ahover307/ninja-receiver-and-timer/Pictures/Wiring Example.jpg

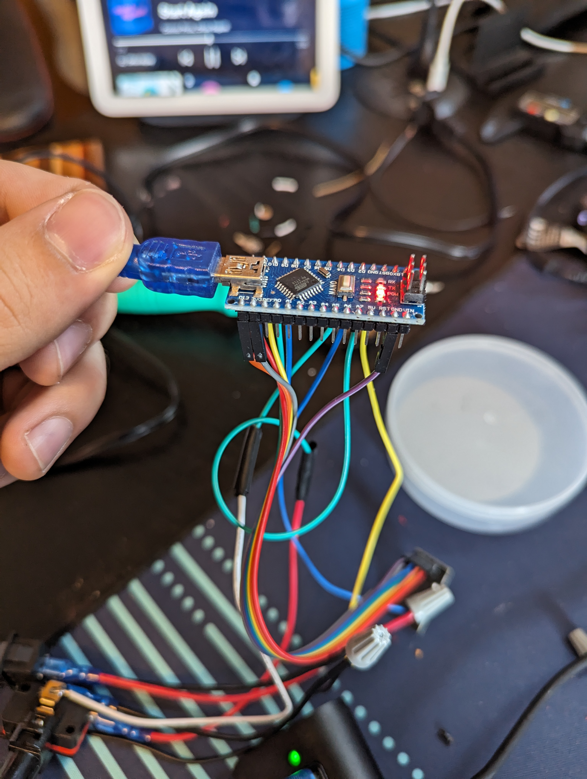
Pictures/Wiring Example.jpg
