ahover307/ninja-receiver-and-timer/Pictures/Test Box.jpg

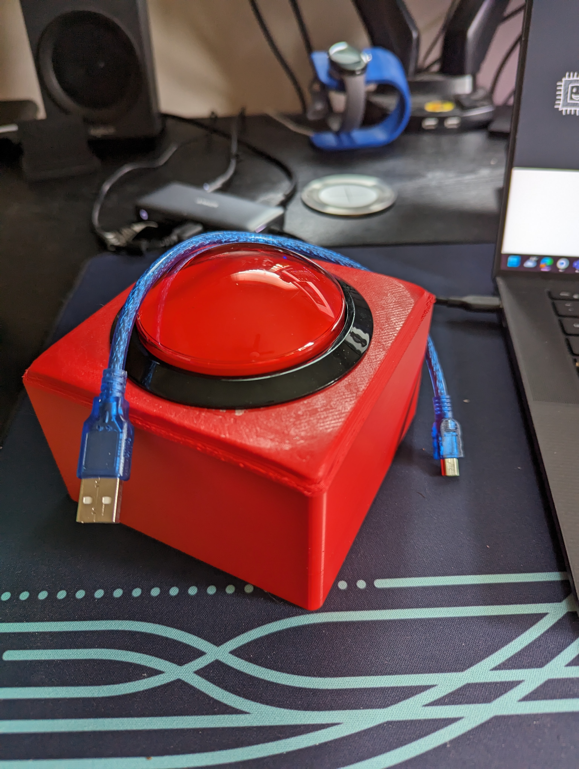
Pictures/Test Box.jpg
