ahover307/ninja-receiver-and-timer/Pictures/Test Fit.jpg

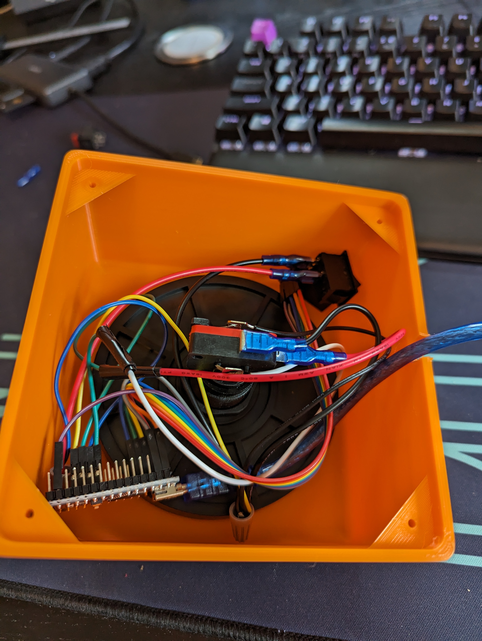
Pictures/Test Fit.jpg
